SrMorrris/Ignotus666-Bluetooth-MIDI-Controller/Super-cobra_devices/Bluetooth Pedalboard_neopixel_1.13/pedalboard mux_4051.jpg

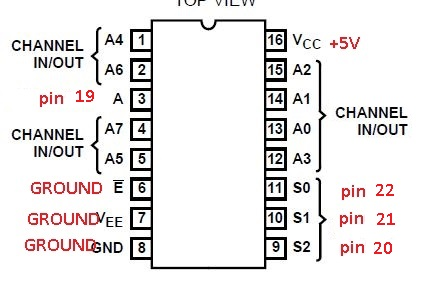
Super-cobra_devices/Bluetooth Pedalboard_neopixel_1.13/pedalboard mux_4051.jpg
